EIT-team/Parallel-CS/schematics/Connector.Filter.Board/sim/eegfilt.asc

C1: cap; 2.2µf
R1: res; 750k
R2: res; 1k
R3: res; 220k
R4: res; 220k
R5: res; 1Meg
U1: opamp2_ad8244; AD8244
U2: opamp2_ad8244; AD8244
U3: opamp2_ad8244; AD8244
U5: UniversalOpamp2
V1: voltage; 5
V3: voltage; SINE(100mV 1 10); AC 1; Rser=10k Cpar=100n
Named nets: VDD, VSS, 0, Vin, Vout
.include AD8244.cir
#.include opamp2_ad8244.asy
;op 1
;tran 1
.meas AVG(V(vout))
.meas AVG(V(vin))
;.ac dec 10 1 10000000
.noise V(Vout) V3 dec 100 1 100k
